PE5PVB/PAL-sign/Firmware/src/testcards/picdream.cpp

// Picdream: colour bars, a black box for the first line (row 144..217,
// x 180..539, between the yellow and blue bars), colour bars again,
// then a multiburst band (row 432..503) reusing multiburst.cpp's exact
// signal, and a last strip of bars. All boundaries even, so none
// flickers between fields.
#include <math.h>
#include <stdint.h>
#include <string.h>

#include "../gfx.h"
#include "../language.h"
#include "../pattern.h"
#include "../rletext.h"
#include "../settings.h"
#include "../textoverlay.h"
#include "picdream_font.h"

static const int BAR_COUNT = 8;
static const int BAR_WORDS = SCREEN_W / 2 / BAR_COUNT;

// Bar boundaries, 90 samples apart: white 0, yellow 90, cyan 180,
// green 270, magenta 360, red 450, blue 540, black 630.
static const int TEXT_X0 = 180;
static const int TEXT_X1 = 540;

static const int TEXT_Y0 = SCREEN_H / 4;
static const int TEXT_PAD = 4;
static int TEXT_Y1;   // set at init from the font's own band

static const int MULTIBURST_Y0 = SCREEN_H * 3 / 4;
static const int MULTIBURST_Y1 = SCREEN_H * 7 / 8;

static uint32_t colourWord[BAR_COUNT];

// The multiburst band, built once at init and replayed per row.
static uint8_t multiburstRow[SCREEN_W * 2];

// One sample of tools/convert_rom_pattern.py's build_frame_multiburst()
// signal (same card multiburst.cpp shows), computed one sample at a
// time rather than into a float[SCREEN_W] buffer first: that would put
// nearly 3kB on the stack at every card change, on a project already
// tight on RAM.
static float multiburstSample(int x) {
  static const float MHZ[6] = {0.5f, 1.0f, 2.0f, 3.0f, 4.0f, 4.8f};
  const float fs = 13.5e6f;
  const float amp = 66.0f;
  const int width = 96, gap = 4, x0 = 112;
  if (x < 48) return 16.0f;
  if (x < 96) return 235.0f;
  if (x >= x0) {
    const int rel = x - x0;
    const int step = width + gap;
    const int k = rel / step;
    const int n = rel % step;
    if (k < 6 && n < width) {
      return 126.0f + amp * sinf(2.0f * (float)M_PI * MHZ[k] * 1.0e6f * (float)n / fs);
    }
  }
  return 126.0f;
}

static void buildMultiburstRow() {
  for (int x = 0; x < SCREEN_W; x++) {
    int v = (int)(multiburstSample(x) + 0.5f);
    if (v < 16) v = 16;
    if (v > 235) v = 235;
    multiburstRow[(x >> 1) * 4 + 1 + (x & 1) * 2] = (uint8_t)v;
  }
  for (int p = 0; p < SCREEN_W / 2; p++) {
    multiburstRow[p * 4 + 0] = 128;   // Cb, monochrome
    multiburstRow[p * 4 + 2] = 128;   // Cr, monochrome
  }
}

static const int LINE_MAX = 32;
static const ContestGlyph *lineG[LINE_MAX];
static int16_t lineX[LINE_MAX];
static int lineN;
static int capRow;
static bool big;      // false: the raster fallback is up
static bool textOn;
static TextOverlay fallback;

static YCbCr lineInk;
static uint8_t lineLut[256];

static void buildLut() {
  lineInk = textInkId();
  for (int i = 0; i < 256; i++) {
    lineLut[i] = (uint8_t)(16 + ((lineInk.Y - 16) * i) / 255);
  }
}

// Folds a character like contestGlyphFor(), indexing PICDREAM_FONT
// instead: a table of its own, used by no other card. The font is 66
// rows, not the contest page's 90 -- a typical callsign does not fit
// the 360-sample box at 90.
static const ContestGlyph *picdreamGlyphFor(const char **pp) {
  const char *p = *pp;
  const uint8_t b = (uint8_t)*p;
  char c;
  if (b == 0xC3 && ((uint8_t)p[1] == 0x98 || (uint8_t)p[1] == 0xB8)) {
    c = 0x01;
    *pp = p + 1;
  } else if (b == 0xD8 || b == 0xF8) {
    c = 0x01;
  } else if (b >= 'a' && b <= 'z') {
    c = (char)(b - 'a' + 'A');
  } else {
    c = (char)b;
  }
  const int n = (int)(sizeof(PICDREAM_FONT) / sizeof(PICDREAM_FONT[0]));
  for (int i = 0; i < n; i++) {
    if (PICDREAM_FONT[i].c == (uint8_t)c) return &PICDREAM_FONT[i];
  }
  return &PICDREAM_FONT[0];
}
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
